JustEnoughDucks/LibreMiG-S/Mechanical/Olukelo Gimbal/stl/gimbal_core_bearing_carrier_pot_side.STL

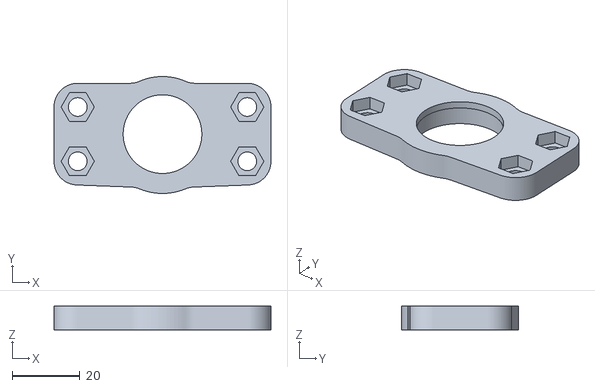
[picture p12: CAD file, 2022-10-17]
Mechanical/Olukelo Gimbal/stl/gimbal_core_bearing_carrier_pot_side.STL
64.0 x 34.5 x 7.00
