JustEnoughDucks/LibreMiG-S/Mechanical/source/assembly/Flip Trigger.FCStd

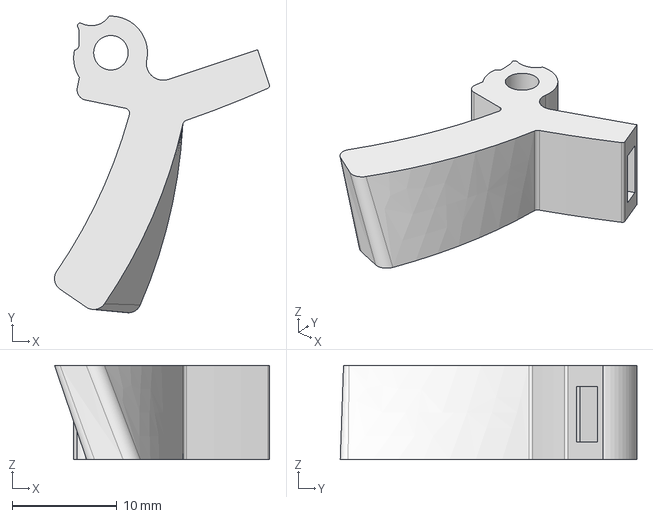
[picture p13: CAD file, 2023-02-02]
Mechanical/source/assembly/Flip Trigger.FCStd
20.6 x 28.4 x 9.00 mm
