JustEnoughDucks/LibreMiG-S/Mechanical/Olukelo Gimbal/solidwork/Bearing.SLDPRT

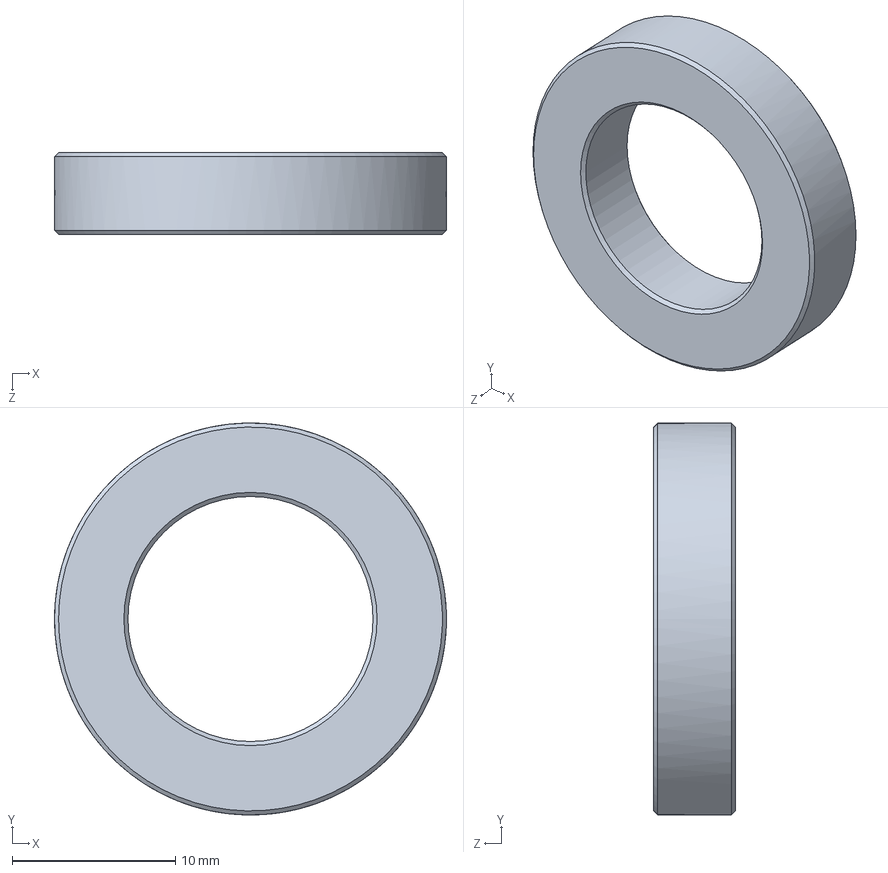
[picture p14: CAD file, 2022-10-17]
Mechanical/Olukelo Gimbal/solidwork/Bearing.SLDPRT
24.0 x 24.0 x 5.00 mm
