JustEnoughDucks/LibreMiG-S/Mechanical/Olukelo Gimbal/stl/gimbal_cam.STL

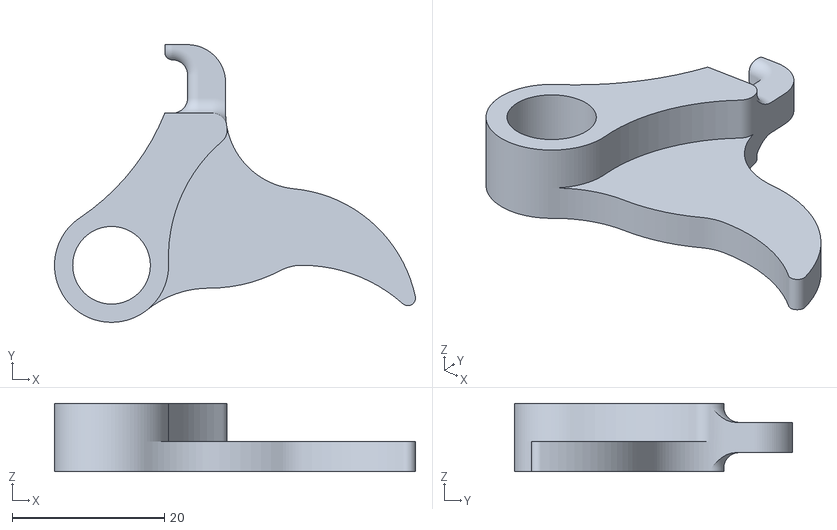
[picture p15: CAD file, 2022-10-17]
Mechanical/Olukelo Gimbal/stl/gimbal_cam.STL
47.5 x 36.5 x 9.00
