JustEnoughDucks/LibreMiG-S/Mechanical/source/assembly/twist_base.FCStd

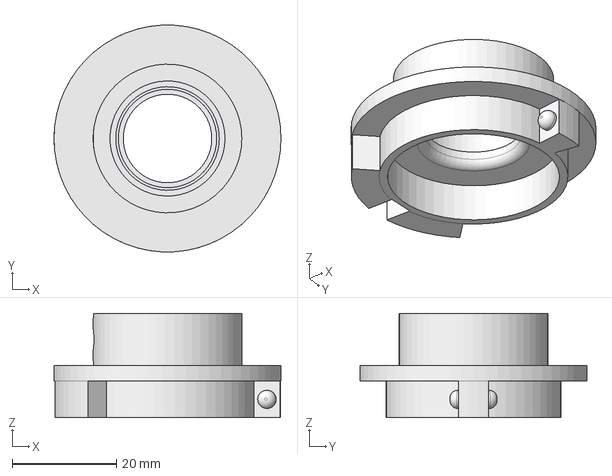
[picture p16: CAD file, 2023-02-02]
Mechanical/source/assembly/twist_base.FCStd
43.6 x 43.5 x 20.0 mm
