JustEnoughDucks/LibreMiG-S/Mechanical/Olukelo Gimbal/stl/gimbal_lever_arm.STL

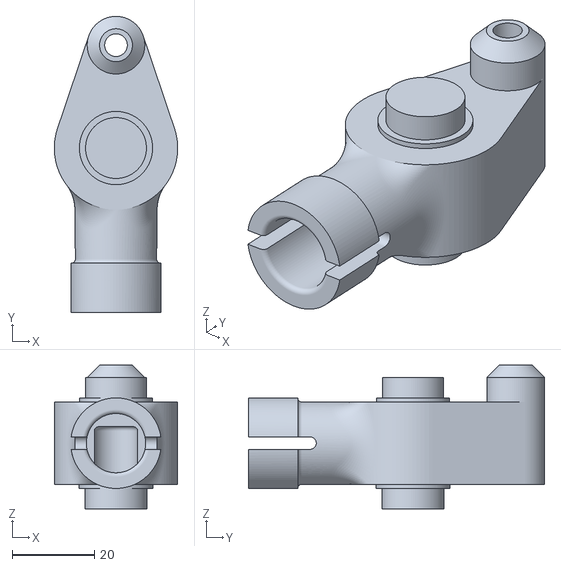
[picture p17: CAD file, 2022-10-17]
Mechanical/Olukelo Gimbal/stl/gimbal_lever_arm.STL
30.0 x 72.0 x 35.0
