JustEnoughDucks/LibreMiG-S/Mechanical/source/assembly/Palm Rest.FCStd

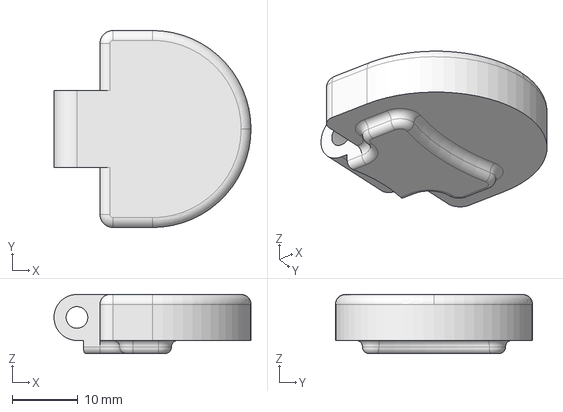
[picture p18: CAD file, 2022-12-05]
Mechanical/source/assembly/Palm Rest.FCStd
30.0 x 30.0 x 9.00 mm
