JustEnoughDucks/LibreMiG-S/Mechanical/Olukelo Gimbal/stl/gimbal_core_bearing_carrier_non_pot_side.STL

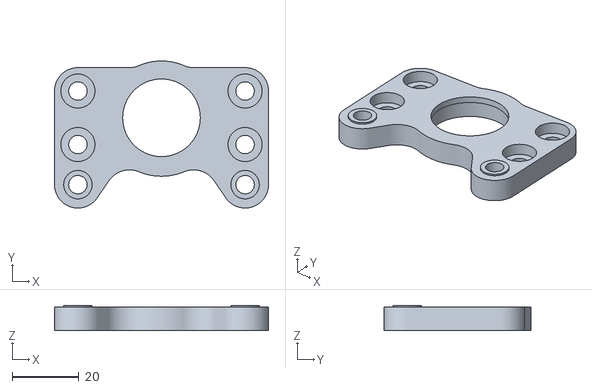
[picture p19: CAD file, 2022-10-17]
Mechanical/Olukelo Gimbal/stl/gimbal_core_bearing_carrier_non_pot_side.STL
64.0 x 44.0 x 7.50
