JustEnoughDucks/LibreMiG-S/Mechanical/source/assembly/TM Adapter.FCStd

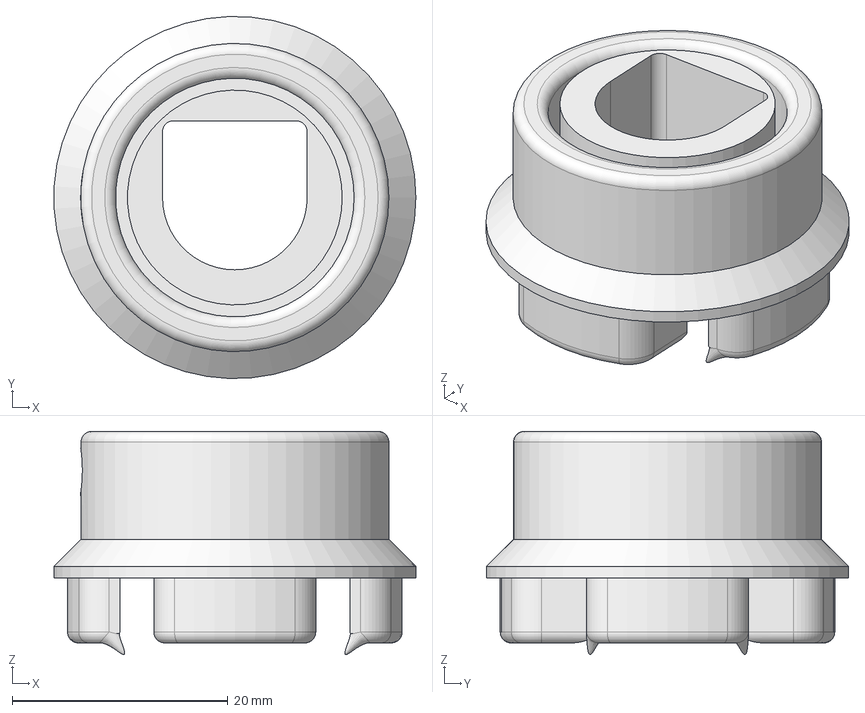
[picture p20: CAD file, 2022-12-05]
Mechanical/source/assembly/TM Adapter.FCStd
33.5 x 33.5 x 20.7 mm
