JustEnoughDucks/LibreMiG-S/Mechanical/source/assembly/Pipe Insert.FCStd

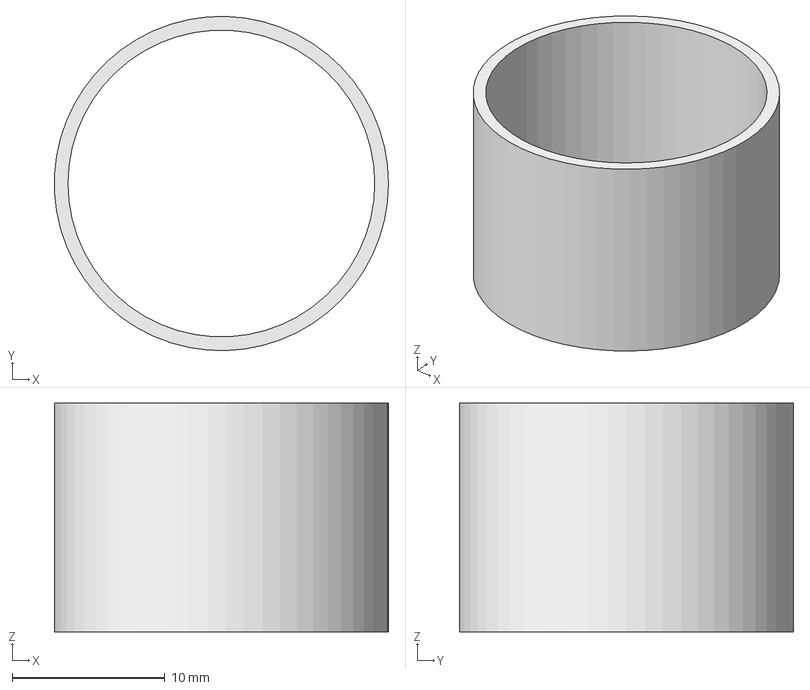
[picture p21: CAD file, 2022-12-05]
Mechanical/source/assembly/Pipe Insert.FCStd
21.9 x 21.9 x 15.0 mm
