JustEnoughDucks/LibreMiG-S/Mechanical/source/assembly/flip_box.FCStd

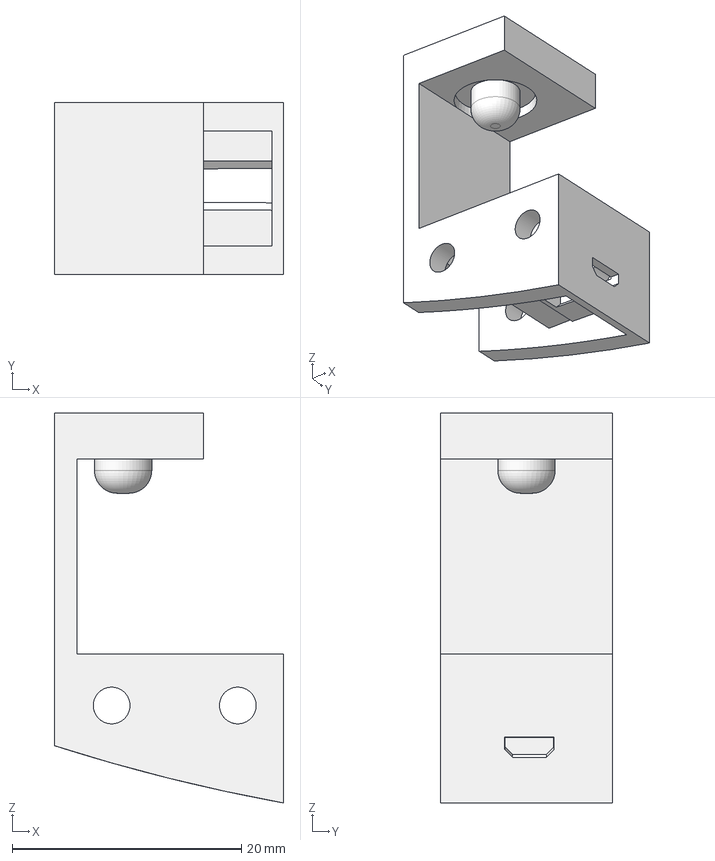
[picture p22: CAD file, 2022-12-05]
Mechanical/source/assembly/flip_box.FCStd
20.0 x 15.0 x 34.0 mm
