JustEnoughDucks/LibreMiG-S/Mechanical/source/assembly/trigger.FCStd

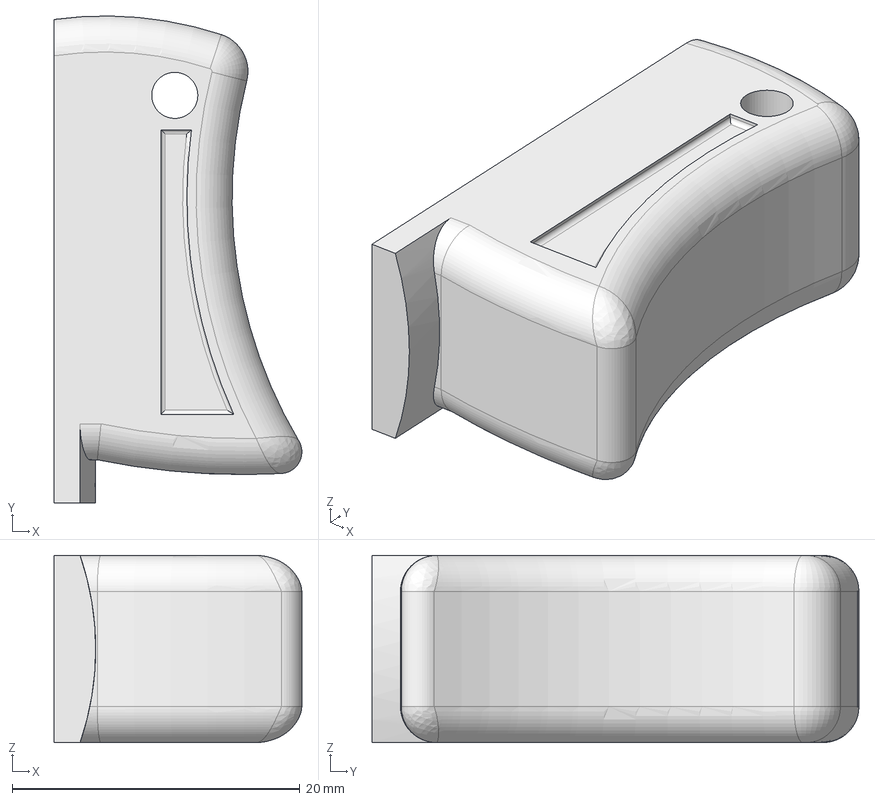
[picture p23: CAD file, 2022-12-05]
Mechanical/source/assembly/trigger.FCStd
17.2 x 33.8 x 13.0 mm
