JustEnoughDucks/LibreMiG-S/Mechanical/source/assembly/Brake Lever.FCStd

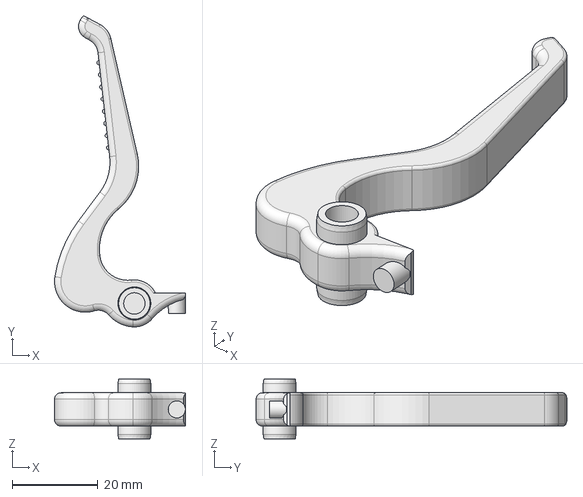
[picture p24: CAD file, 2022-12-05]
Mechanical/source/assembly/Brake Lever.FCStd
30.6 x 72.6 x 14.0 mm
