JustEnoughDucks/LibreMiG-S/Mechanical/source/assembly/Flip Plank.FCStd

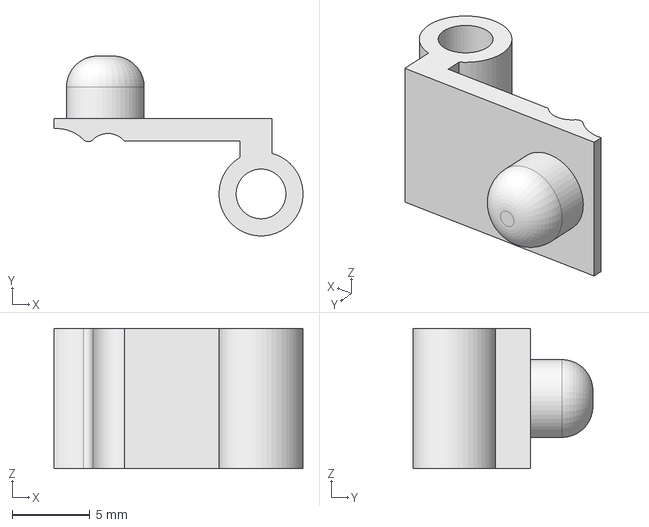
[picture p25: CAD file, 2022-12-05]
Mechanical/source/assembly/Flip Plank.FCStd
16.0 x 11.6 x 9.00 mm
