JustEnoughDucks/LibreMiG-S/Mechanical/source/assembly/RKJXV1220001.FCStd

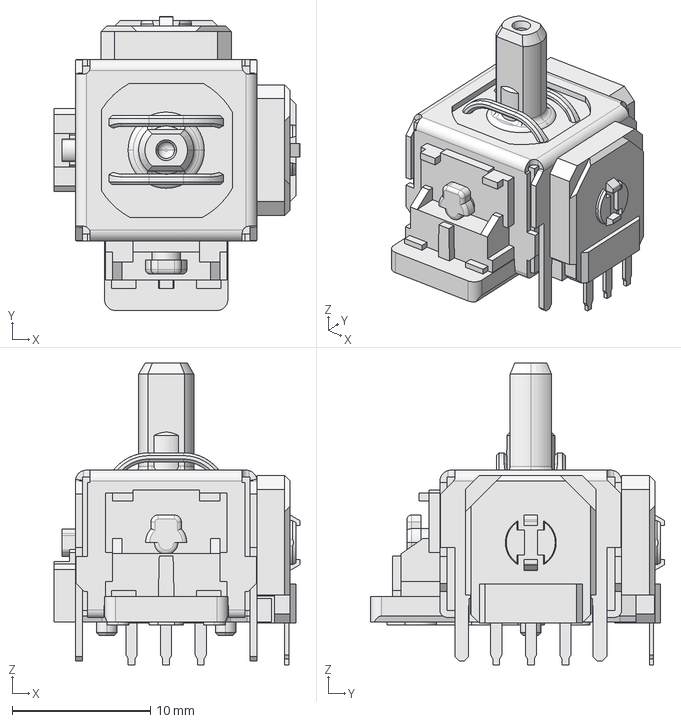
[picture p26: CAD file, 2022-12-05]
Mechanical/source/assembly/RKJXV1220001.FCStd
17.8 x 21.3 x 21.9 mm
