JustEnoughDucks/LibreMiG-S/Mechanical/source/assembly/rkjxt1f42001.FCStd

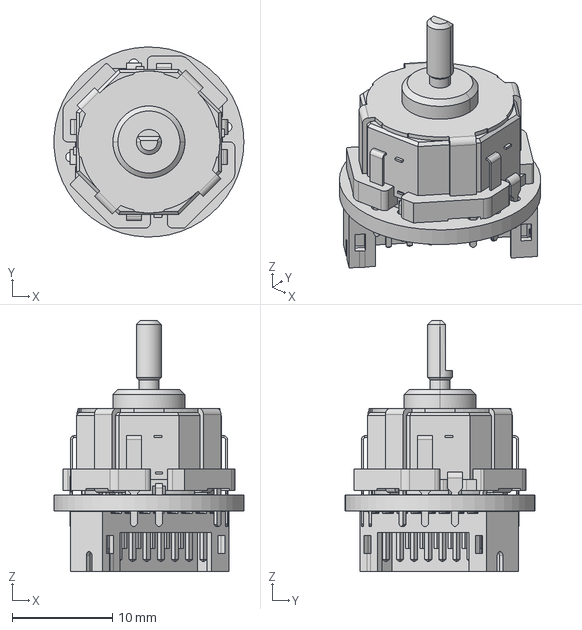
[picture p27: CAD file, 2022-12-05]
Mechanical/source/assembly/rkjxt1f42001.FCStd
19.0 x 19.0 x 25.1 mm
